hackup/Pi1541io/media/Pi1541io-rev1.jpg

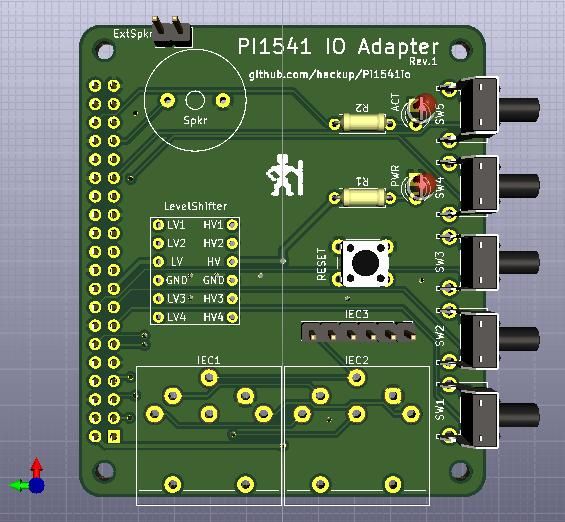
media/Pi1541io-rev1.jpg
