hackup/Pi1541io/media/Pi1541io-rev1-assembled.jpg

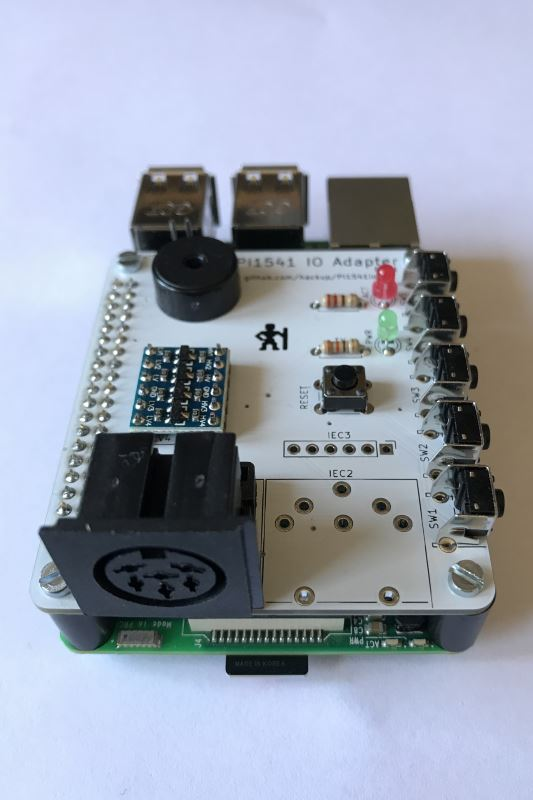
media/Pi1541io-rev1-assembled.jpg
